CircuitMonkey/epoch/Firmware/epoch-fw/glyphs.h

#include <sys/_stdint.h>
// [glyph16g]  glyph  16x16   greyscale  as nybles
#ifndef Glyphs_h 
#define Glyphs_h

#define G_WH 16

static const unsigned char PROGMEM glyph16m_blank[] = { 
  0b00000000, 0b00000000,
  0b00000000, 0b00000000,
  0b00000000, 0b00000000,
  0b00000000, 0b00000000,
  0b00000000, 0b00000000,
  0b00000000, 0b00000000,
  0b00000000, 0b00000000,
  0b00000000, 0b00000000,
  0b00000000, 0b00000000,
  0b00000000, 0b00000000,
  0b00000000, 0b00000000,
  0b00000000, 0b00000000,
  0b00000000, 0b00000000,
  0b00000000, 0b00000000,
  0b00000000, 0b00000000,
  0b00000000, 0b00000000 
};
static const unsigned char PROGMEM glyph16m_x[] = { 
  0b10000000, 0b00000001,
  0b01000000, 0b00000010,
  0b00100000, 0b00000100,
  0b00010000, 0b00001000,
  0b00001000, 0b00010000,
  0b00000100, 0b00100000,
  0b00000010, 0b01000000,
  0b00000001, 0b10000000,
  0b00000001, 0b10000000,
  0b00000010, 0b01000000,
  0b00000100, 0b00100000,
  0b00001000, 0b00010000,
  0b00010000, 0b00001000,
  0b00100000, 0b00000100,
  0b01000000, 0b00000010,
  0b10000000, 0b00000001 
};
static const unsigned char PROGMEM glyph48m_blank[] = { 
  0b00000000, 0b00000000, 0b00000000, 0b00000000, 0b00000000, 0b00000000,
  0b00000000, 0b00000000, 0b00000000, 0b00000000, 0b00000000, 0b00000000,
  0b00000000, 0b00000000, 0b00000000, 0b00000000, 0b00000000, 0b00000000,
  0b00000000, 0b00000000, 0b00000000, 0b00000000, 0b00000000, 0b00000000,
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
  0b00000000, 0b00000111, 0b11000000, 0b00000111, 0b11000000, 0b00000000,
  0b00000000, 0b00000111, 0b11000000, 0b00000111, 0b11000000, 0b00000000,
  0b00000000, 0b00000111, 0b11000000, 0b00000111, 0b11000000, 0b00000000
};


#endif
